JellyTitan/ErgoDonk-Zero/docs/images/1N4001_diode_bending-250w.webp

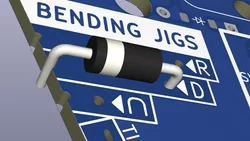
docs/images/1N4001_diode_bending-250w.webp
