JellyTitan/ErgoDonk-Zero/docs/images/3d_model_of_work_feet-250w.webp

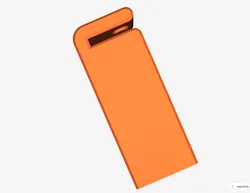
docs/images/3d_model_of_work_feet-250w.webp
