JellyTitan/ErgoDonk-Zero/docs/images/acrylic_case/acrylic_handsome_stack-250w.webp

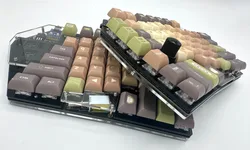
docs/images/acrylic_case/acrylic_handsome_stack-250w.webp
