JellyTitan/ErgoDonk-Zero/docs/images/acrylic_case/acrylic_lh_mcu_cover-400w.webp

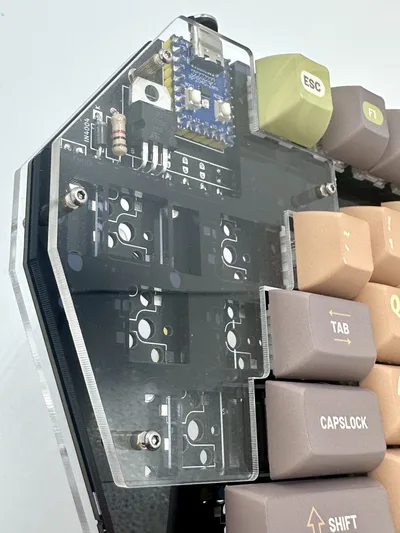
docs/images/acrylic_case/acrylic_lh_mcu_cover-400w.webp
