JellyTitan/ErgoDonk-Zero/docs/images/acrylic_case/acrylic_rh_mcu_cover-250w.webp

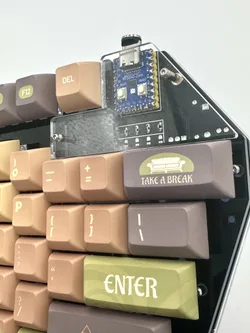
docs/images/acrylic_case/acrylic_rh_mcu_cover-250w.webp
