JellyTitan/ErgoDonk-Zero/docs/images/acrylic_case/acrylic_tilted_hero-250w.webp

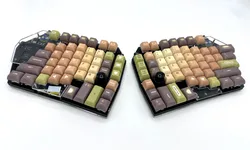
docs/images/acrylic_case/acrylic_tilted_hero-250w.webp
