JellyTitan/ErgoDonk-Zero/docs/images/acrylic_case/backplate-250w.webp

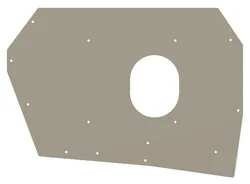
docs/images/acrylic_case/backplate-250w.webp
