JellyTitan/ErgoDonk-Zero/docs/images/acrylic_case/bumper_locations-250w.webp

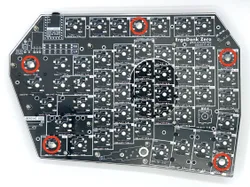
docs/images/acrylic_case/bumper_locations-250w.webp
