JellyTitan/ErgoDonk-Zero/docs/images/acrylic_case/keyplate-250w.webp

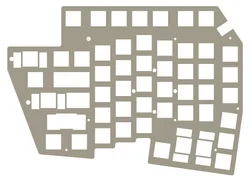
docs/images/acrylic_case/keyplate-250w.webp
