JellyTitan/ErgoDonk-Zero/docs/images/acrylic_case/knob_close_up-800w.webp

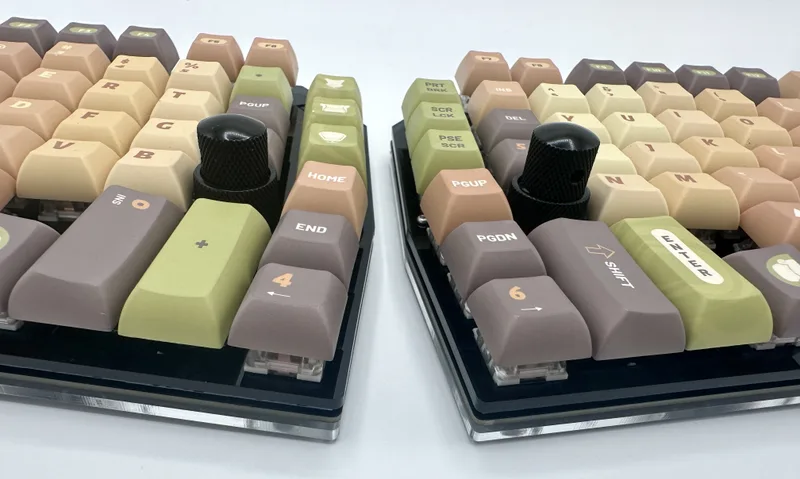
docs/images/acrylic_case/knob_close_up-800w.webp
