JellyTitan/ErgoDonk-Zero/docs/images/acrylic_case/LH_MCU_cover-150w.webp

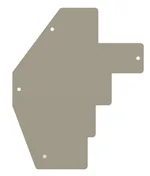
docs/images/acrylic_case/LH_MCU_cover-150w.webp
