JellyTitan/ErgoDonk-Zero/docs/images/acrylic_case/m2_9mm_standoff-250w.webp

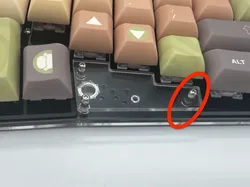
docs/images/acrylic_case/m2_9mm_standoff-250w.webp
