JellyTitan/ErgoDonk-Zero/docs/images/acrylic_case/m2_9mm_standoff.png

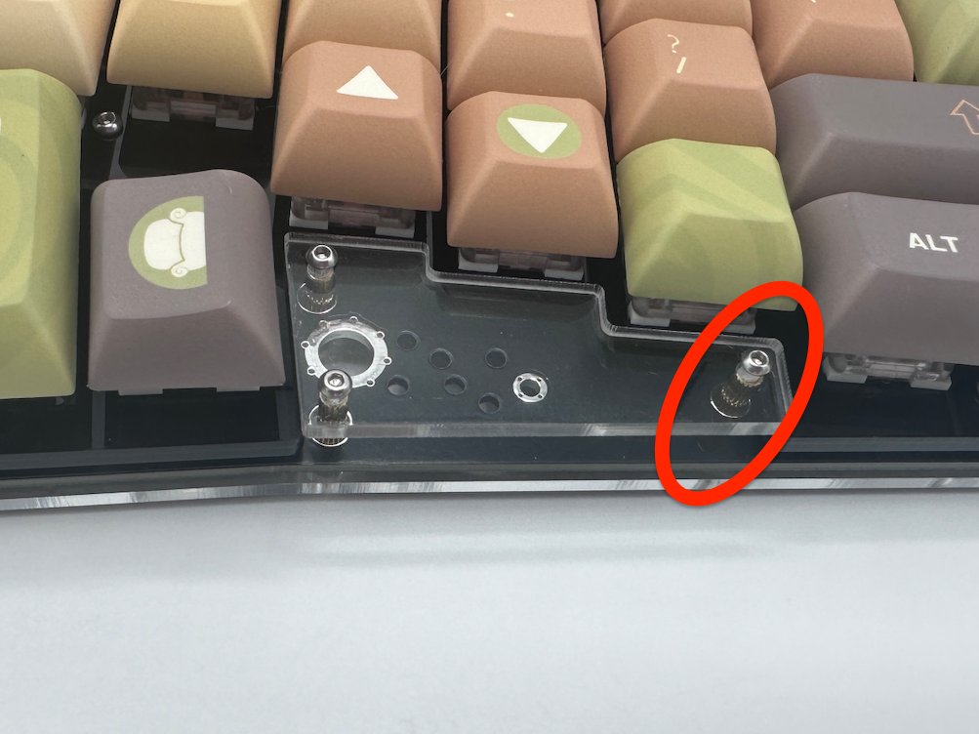
docs/images/acrylic_case/m2_9mm_standoff.png
