JellyTitan/ErgoDonk-Zero/docs/images/acrylic_case/m2_16mm_standoff.png

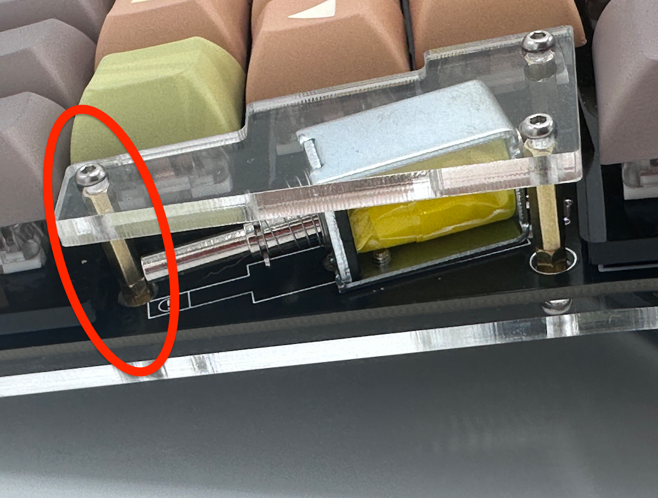
docs/images/acrylic_case/m2_16mm_standoff.png
