JellyTitan/ErgoDonk-Zero/docs/images/acrylic_case/RH_MCU_cover-400w.webp

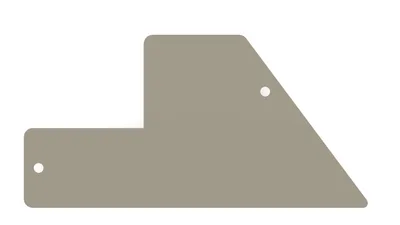
docs/images/acrylic_case/RH_MCU_cover-400w.webp
