JellyTitan/ErgoDonk-Zero/docs/images/acrylic_case/solenoid_blank_cover_plate_RH-1200w.webp

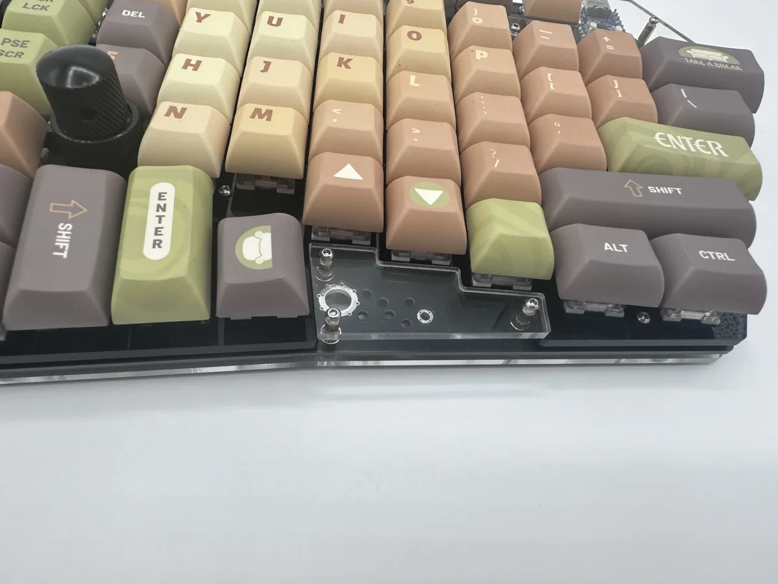
docs/images/acrylic_case/solenoid_blank_cover_plate_RH-1200w.webp
