JellyTitan/ErgoDonk-Zero/docs/images/acrylic_case/solenoid_cover-250w.webp

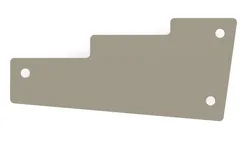
docs/images/acrylic_case/solenoid_cover-250w.webp
