JellyTitan/ErgoDonk-Zero/docs/images/acrylic_case/solenoid_cover_plate_LH-1600w.webp

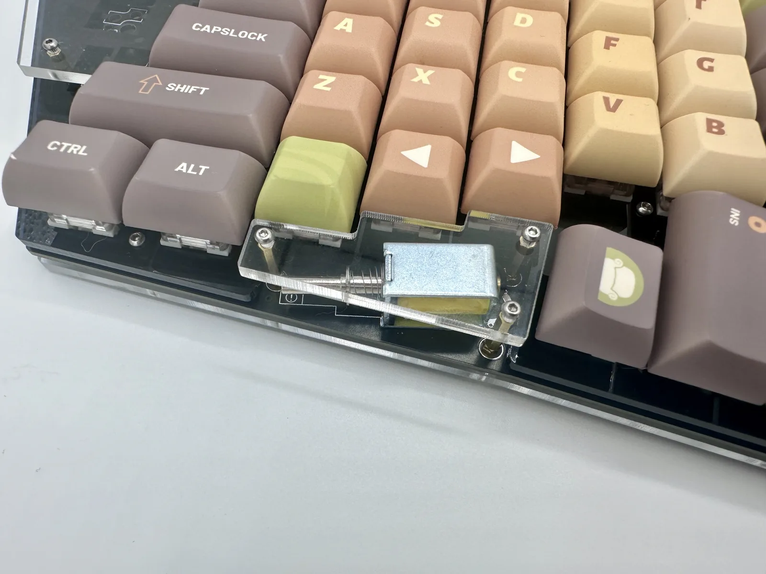
docs/images/acrylic_case/solenoid_cover_plate_LH-1600w.webp
