JellyTitan/ErgoDonk-Zero/docs/images/asymmetrical_diode_marking-250w.webp

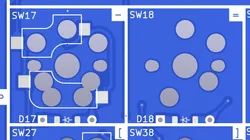
docs/images/asymmetrical_diode_marking-250w.webp
