JellyTitan/ErgoDonk-Zero/docs/images/asymmetrical_diode_marking.webp

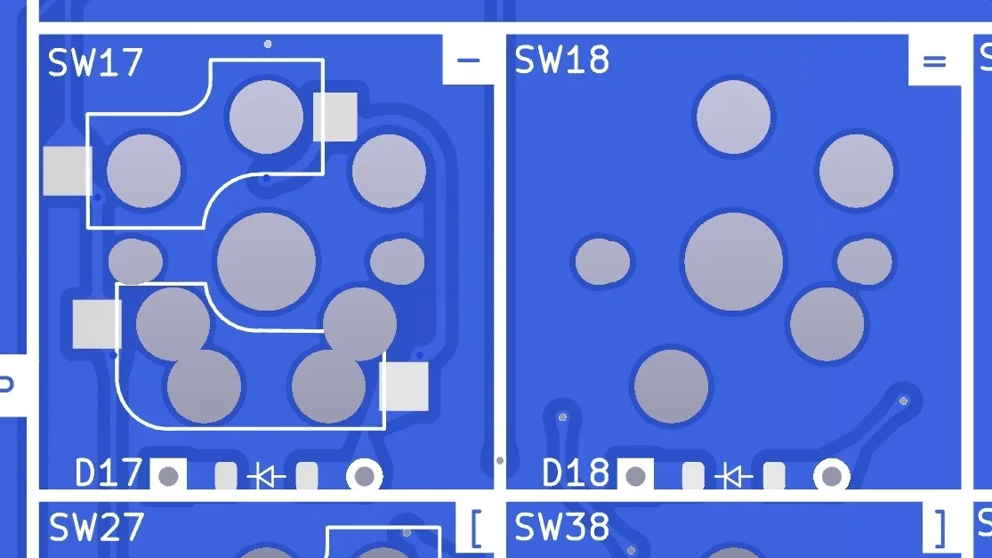
docs/images/asymmetrical_diode_marking.webp
