JellyTitan/ErgoDonk-Zero/docs/images/carpenter_pencil-250w.webp

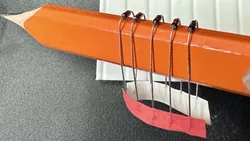
docs/images/carpenter_pencil-250w.webp
