JellyTitan/ErgoDonk-Zero/docs/images/clipping_jumpers-150w.webp

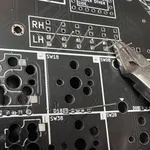
docs/images/clipping_jumpers-150w.webp
