JellyTitan/ErgoDonk-Zero/docs/images/diode_bend_top-1200w.webp

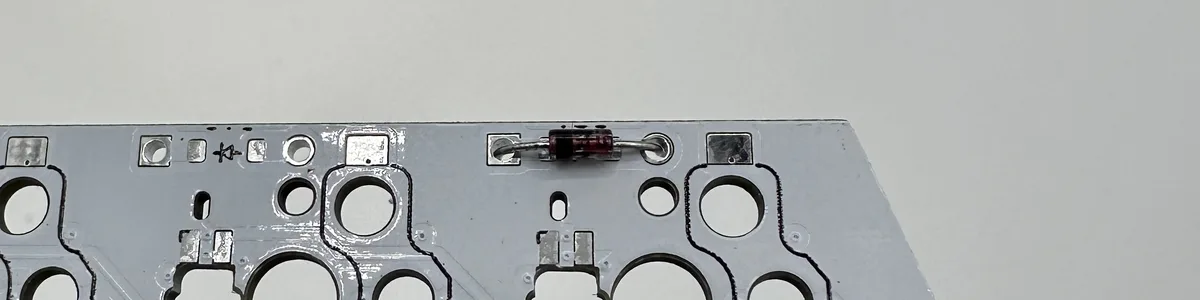
docs/images/diode_bend_top-1200w.webp
