JellyTitan/ErgoDonk-Zero/docs/images/diode_bend_under-800w.webp

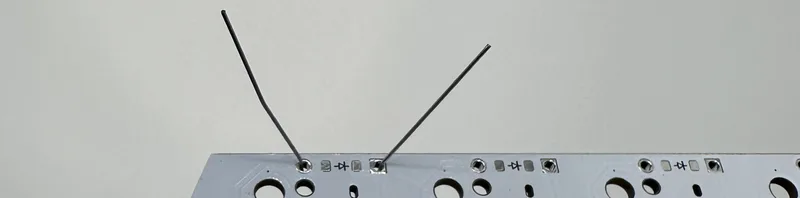
docs/images/diode_bend_under-800w.webp
