JellyTitan/ErgoDonk-Zero/docs/images/diode_jig_cut-400w.webp

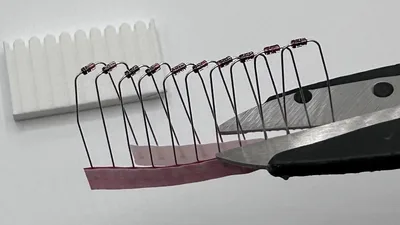
docs/images/diode_jig_cut-400w.webp
