JellyTitan/ErgoDonk-Zero/docs/images/diode_jig_fold-250w.webp

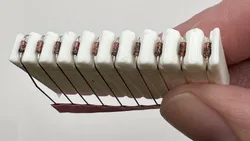
docs/images/diode_jig_fold-250w.webp
