JellyTitan/ErgoDonk-Zero/docs/images/diodes-150w.webp

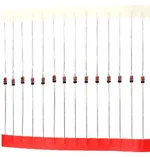
docs/images/diodes-150w.webp
