JellyTitan/ErgoDonk-Zero/docs/images/ec11-150w.webp

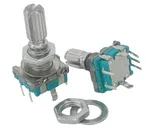
docs/images/ec11-150w.webp
