JellyTitan/ErgoDonk-Zero/docs/images/ec11_knob-450w.webp

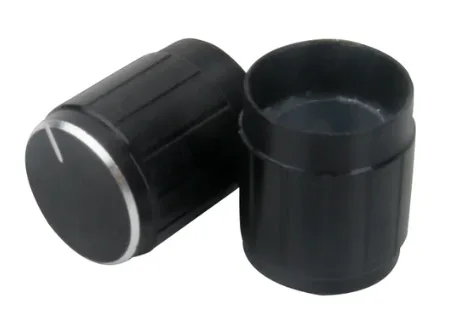
docs/images/ec11_knob-450w.webp
