JellyTitan/ErgoDonk-Zero/docs/images/ergodonk_bristling_with_diodes-800w.webp

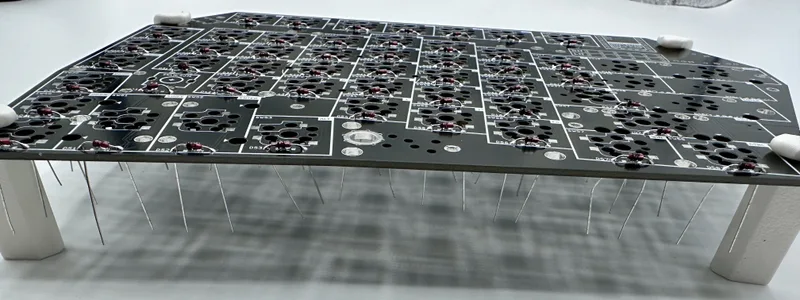
docs/images/ergodonk_bristling_with_diodes-800w.webp
