JellyTitan/ErgoDonk-Zero/docs/images/ergodonk_lh_sockets-1600w.webp

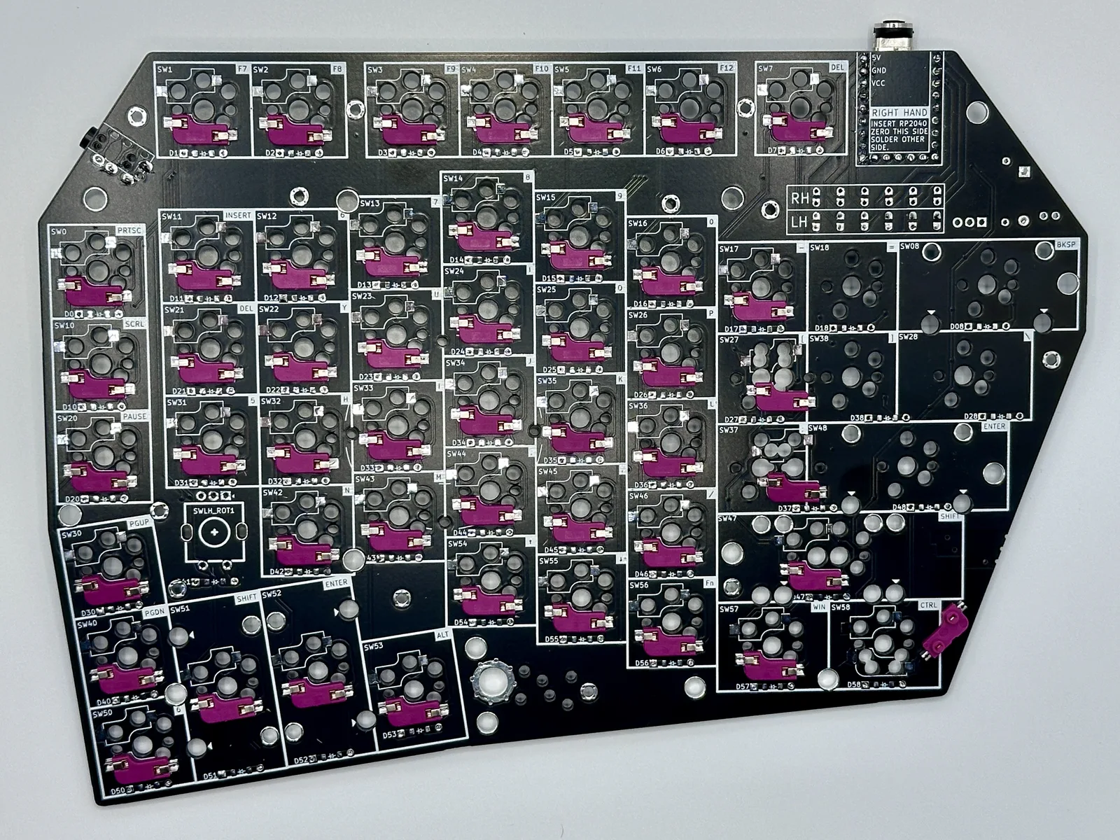
docs/images/ergodonk_lh_sockets-1600w.webp
