JellyTitan/ErgoDonk-Zero/docs/images/ergodonk_monobody_case-250w.webp

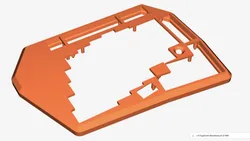
docs/images/ergodonk_monobody_case-250w.webp
