JellyTitan/ErgoDonk-Zero/docs/images/ergodonk_rh_sockets-250w.webp

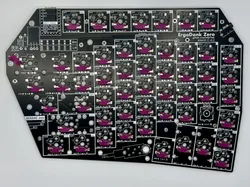
docs/images/ergodonk_rh_sockets-250w.webp
