JellyTitan/ErgoDonk-Zero/docs/images/ErgoDonk_row_heights-400w.webp

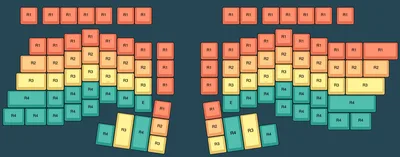
docs/images/ErgoDonk_row_heights-400w.webp
