JellyTitan/ErgoDonk-Zero/docs/images/ErgoDonk_zero_all_feet-400w.webp

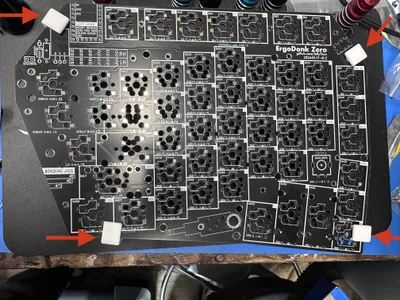
docs/images/ErgoDonk_zero_all_feet-400w.webp
