JellyTitan/ErgoDonk-Zero/docs/images/ergodonk_zero_keyplate-400w.webp

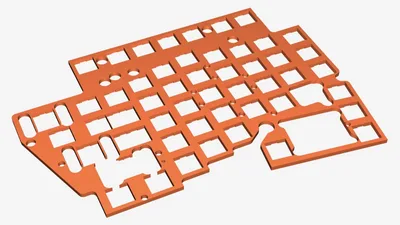
docs/images/ergodonk_zero_keyplate-400w.webp
