JellyTitan/ErgoDonk-Zero/docs/images/Ergodonk_zero_one_foot-4032w.webp

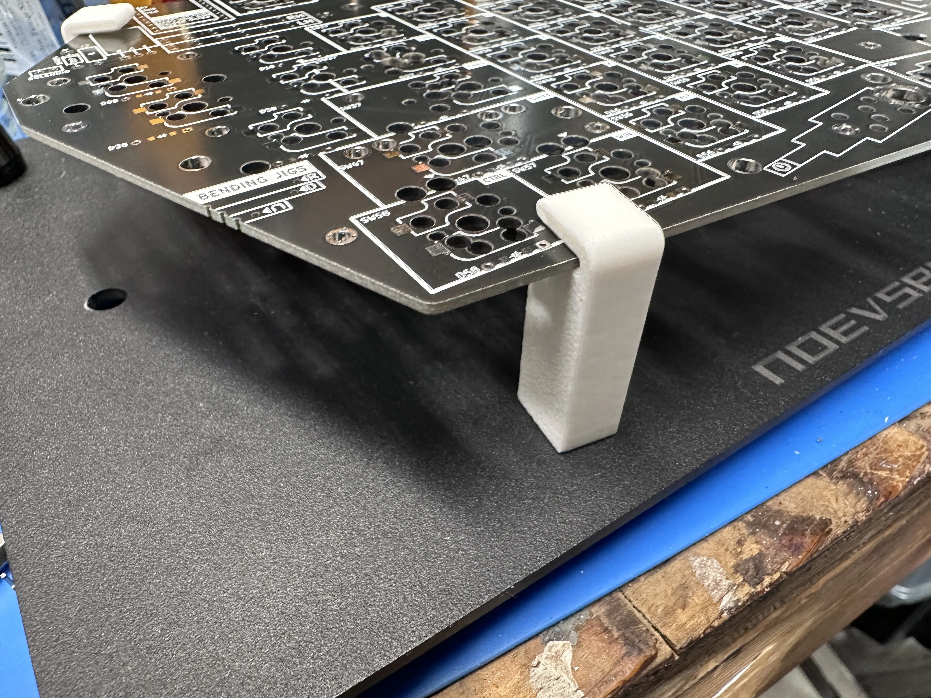
docs/images/Ergodonk_zero_one_foot-4032w.webp
