JellyTitan/ErgoDonk-Zero/docs/images/fdm_case/fdm_donk_2-400w.webp

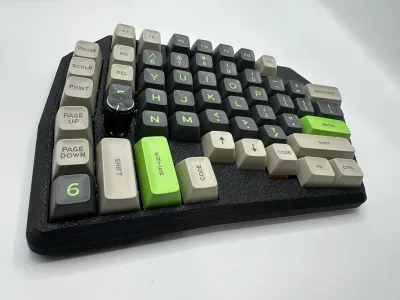
docs/images/fdm_case/fdm_donk_2-400w.webp
