JellyTitan/ErgoDonk-Zero/docs/images/fdm_case/fdm_donk_3-250w.webp

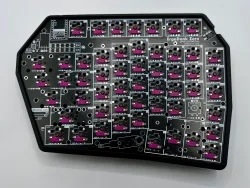
docs/images/fdm_case/fdm_donk_3-250w.webp
