JellyTitan/ErgoDonk-Zero/docs/images/fdm_case/fdm_donk_cases_hero.jpeg

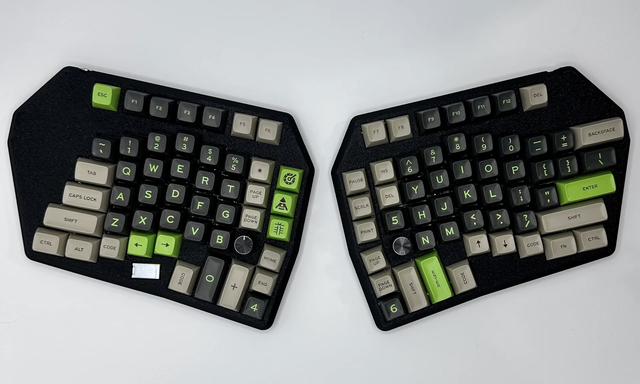
docs/images/fdm_case/fdm_donk_cases_hero.jpeg
