JellyTitan/ErgoDonk-Zero/docs/images/hot_swop_sockets-250w.webp

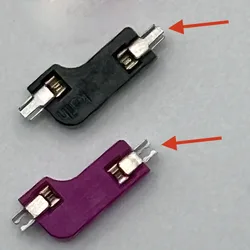
docs/images/hot_swop_sockets-250w.webp
