JellyTitan/ErgoDonk-Zero/docs/images/jumper_bender_use-150w.webp

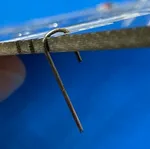
docs/images/jumper_bender_use-150w.webp
