JellyTitan/ErgoDonk-Zero/docs/images/jumpers-208w.webp

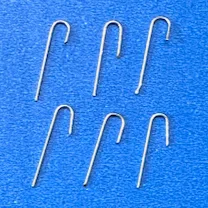
docs/images/jumpers-208w.webp
