JellyTitan/ErgoDonk-Zero/docs/images/jumpers_in_place-400w.webp

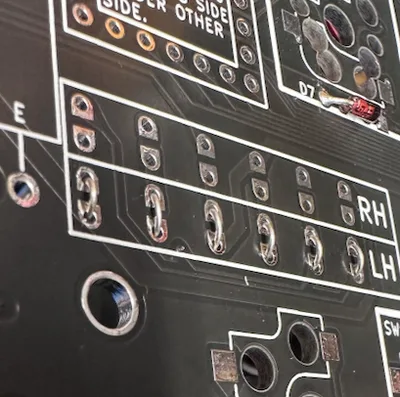
docs/images/jumpers_in_place-400w.webp
