JellyTitan/ErgoDonk-Zero/docs/images/kapton_under-1600w.webp

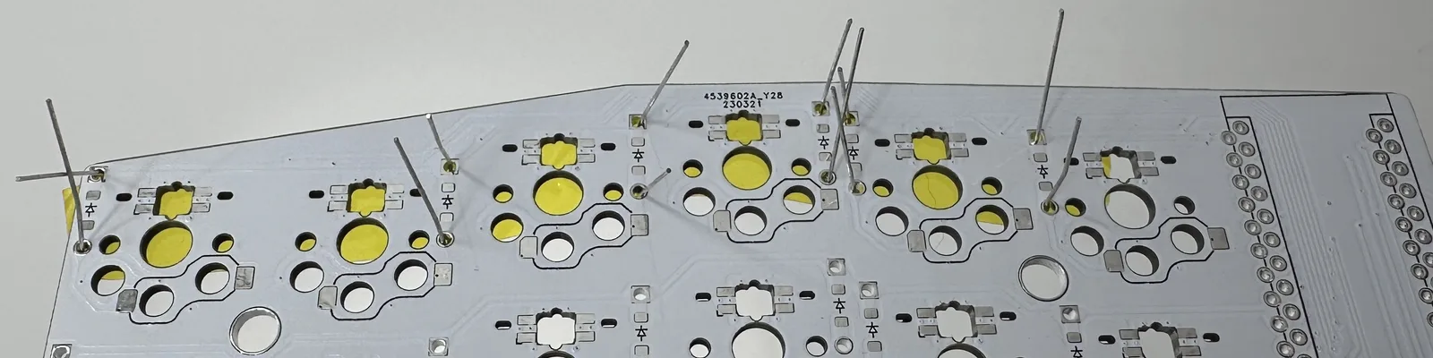
docs/images/kapton_under-1600w.webp
