JellyTitan/ErgoDonk-Zero/docs/images/LH_backside_diode-1600w.webp

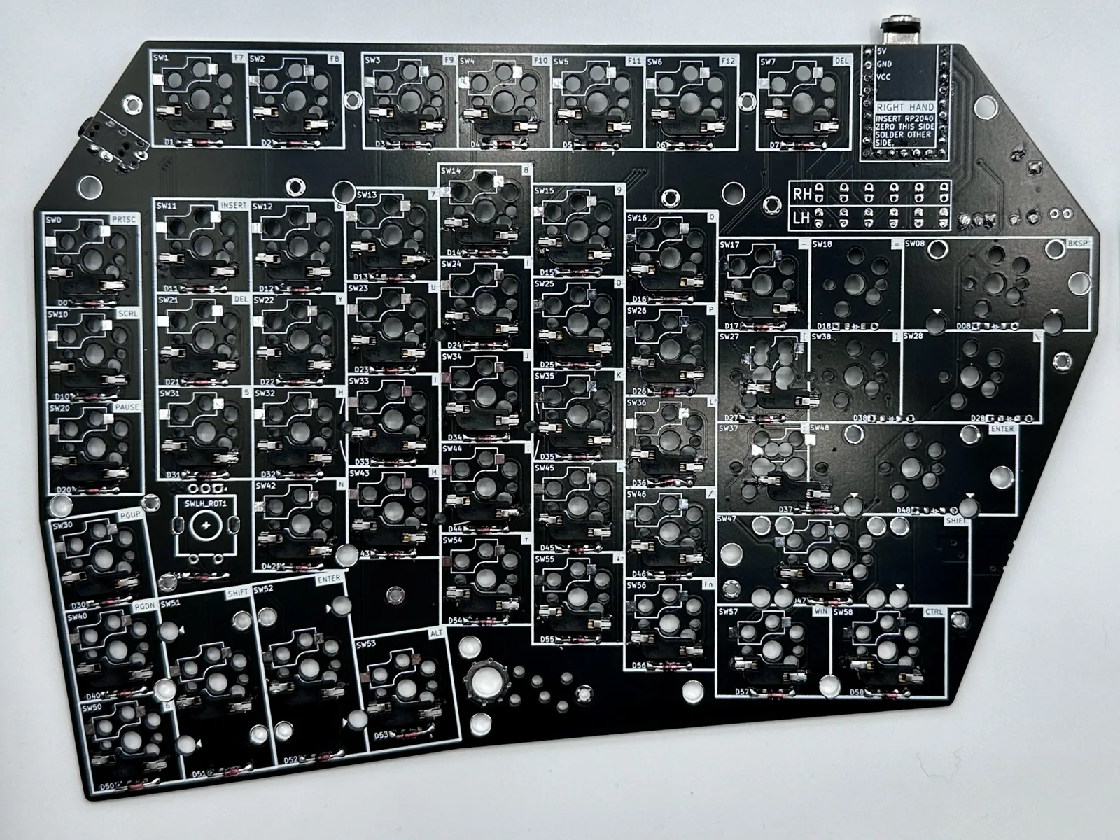
docs/images/LH_backside_diode-1600w.webp
