JellyTitan/ErgoDonk-Zero/docs/images/line_up_the_zero-250w.webp

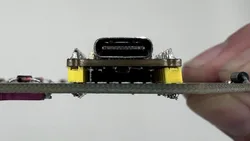
docs/images/line_up_the_zero-250w.webp
