JellyTitan/ErgoDonk-Zero/docs/images/mcu_top_of_board_1-250w.webp

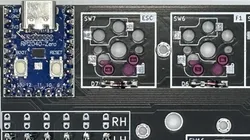
docs/images/mcu_top_of_board_1-250w.webp
