JellyTitan/ErgoDonk-Zero/docs/images/mcu_top_of_board_2-1200w.webp

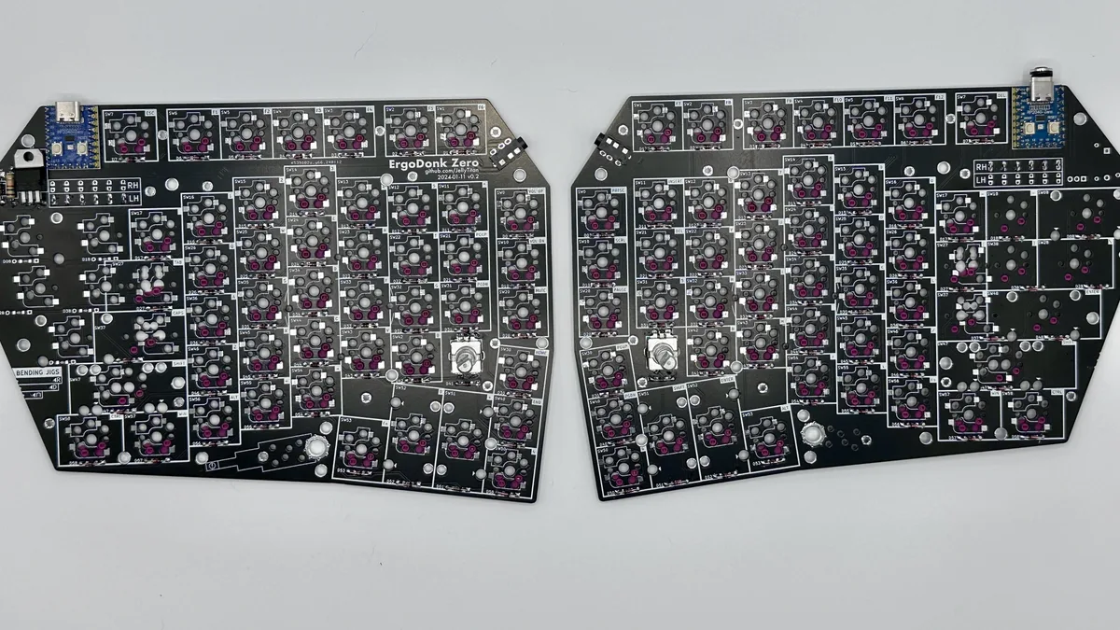
docs/images/mcu_top_of_board_2-1200w.webp
