JellyTitan/ErgoDonk-Zero/docs/images/mvp_case/mvp_case_back-250w.webp

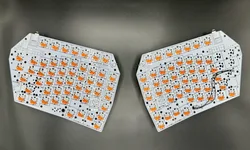
docs/images/mvp_case/mvp_case_back-250w.webp
