JellyTitan/ErgoDonk-Zero/docs/images/mvp_case/mvp_case_both-800w.webp

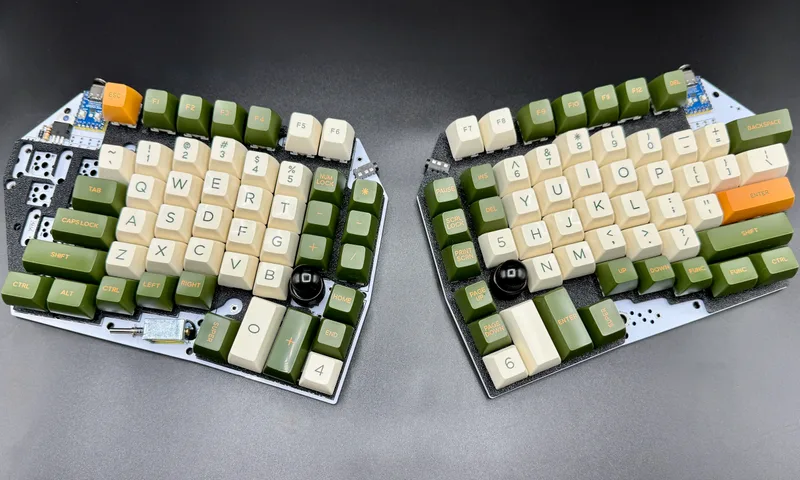
docs/images/mvp_case/mvp_case_both-800w.webp
