JellyTitan/ErgoDonk-Zero/docs/images/mvp_case/mvp_case_left_closeup-250w.webp

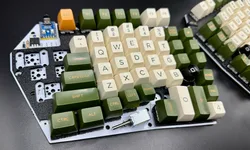
docs/images/mvp_case/mvp_case_left_closeup-250w.webp
