JellyTitan/ErgoDonk-Zero/docs/images/pad_nub-175w.webp

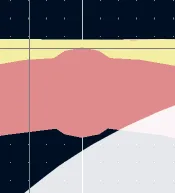
docs/images/pad_nub-175w.webp
