JellyTitan/ErgoDonk-Zero/docs/images/qmk/ergodonk_zero_qmk_default_keymap.png

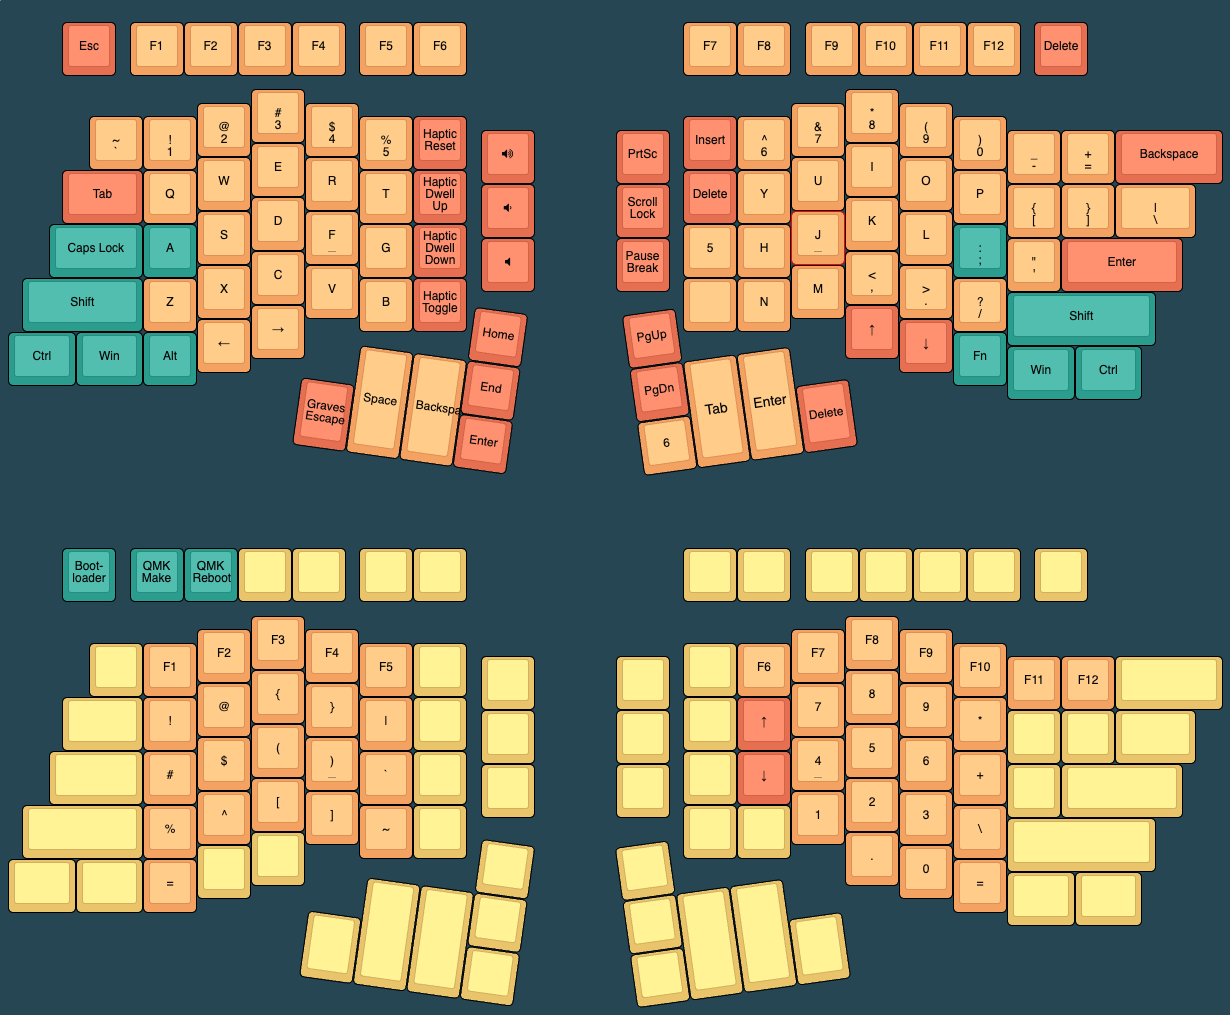
docs/images/qmk/ergodonk_zero_qmk_default_keymap.png
