JellyTitan/ErgoDonk-Zero/docs/images/resistor_bending-400w.webp

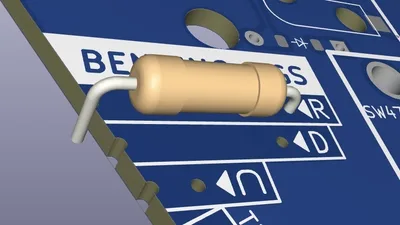
docs/images/resistor_bending-400w.webp
