JellyTitan/ErgoDonk-Zero/docs/images/RH_backside_diode-1200w.webp

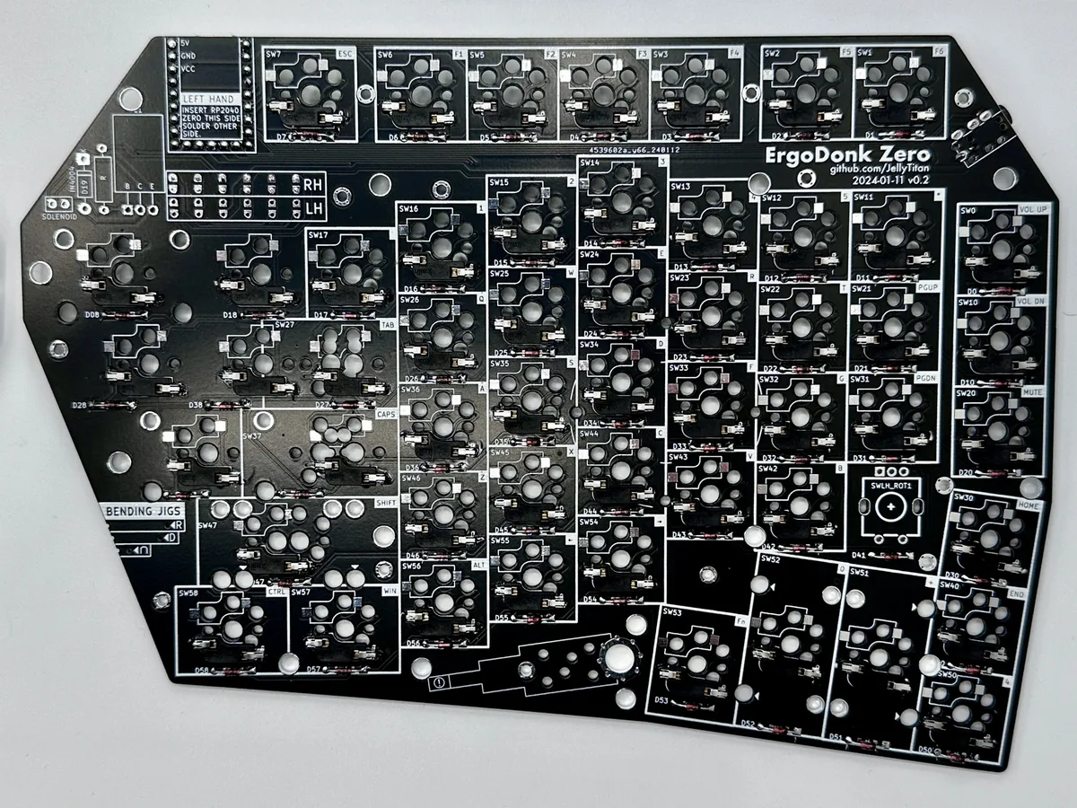
docs/images/RH_backside_diode-1200w.webp
