JellyTitan/ErgoDonk-Zero/docs/images/rp2040-250w.webp

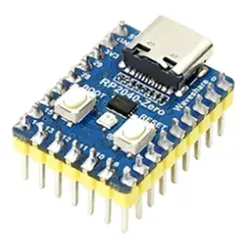
docs/images/rp2040-250w.webp
