JellyTitan/ErgoDonk-Zero/docs/images/sa_heights-400w.webp

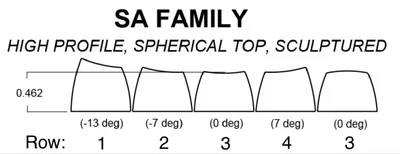
docs/images/sa_heights-400w.webp
