JellyTitan/ErgoDonk-Zero/docs/images/solenoid_circuit-1200w.webp

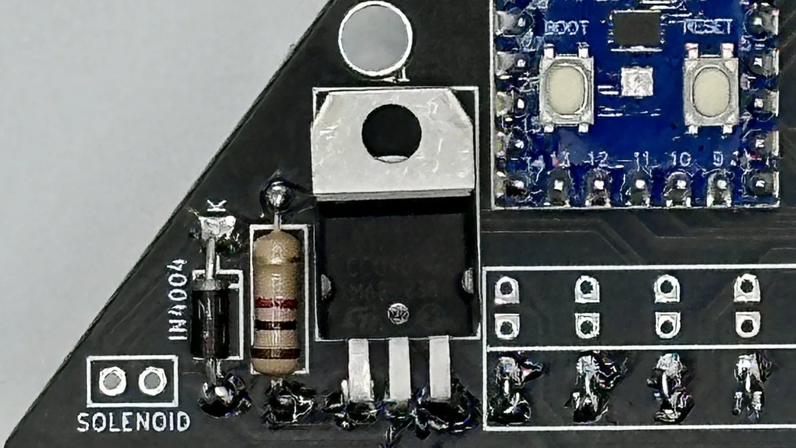
docs/images/solenoid_circuit-1200w.webp
