JellyTitan/ErgoDonk-Zero/docs/images/solenoid_circuit_tip120-250w.webp

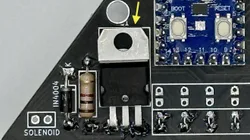
docs/images/solenoid_circuit_tip120-250w.webp
