JellyTitan/ErgoDonk-Zero/docs/images/Solenoid_on_front-1600w.webp

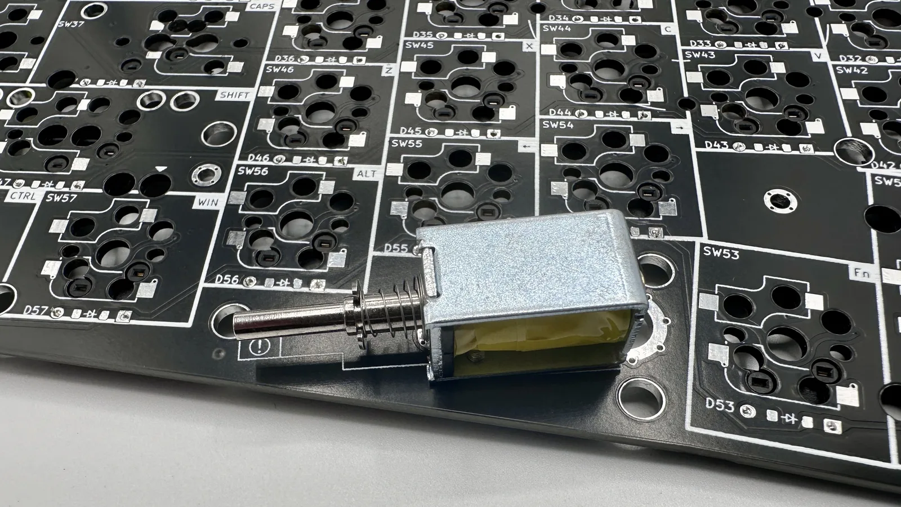
docs/images/Solenoid_on_front-1600w.webp
