JellyTitan/ErgoDonk-Zero/docs/images/solenoid_pin_nipping-400w.webp

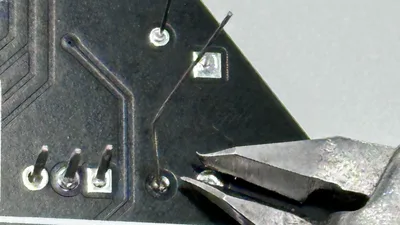
docs/images/solenoid_pin_nipping-400w.webp
