JellyTitan/ErgoDonk-Zero/docs/images/solenoids-250w.webp

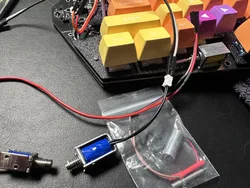
docs/images/solenoids-250w.webp
