JellyTitan/ErgoDonk-Zero/docs/images/stab_prob-250w.webp

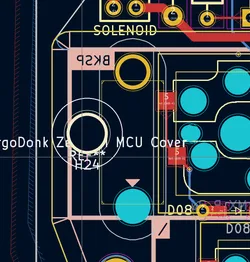
docs/images/stab_prob-250w.webp
