JellyTitan/ErgoDonk-Zero/docs/images/stabilizer_markings-811w.webp

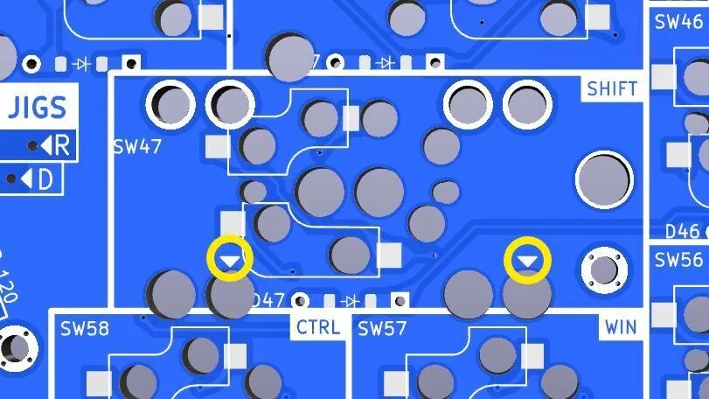
docs/images/stabilizer_markings-811w.webp
