JellyTitan/ErgoDonk-Zero/docs/images/thumb_stabs-250w.webp

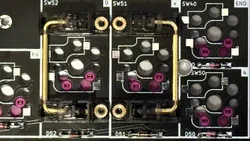
docs/images/thumb_stabs-250w.webp
