JellyTitan/ErgoDonk-Zero/docs/images/tip_120_jig_front-250w.webp

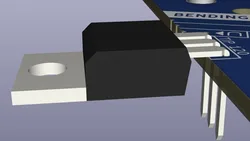
docs/images/tip_120_jig_front-250w.webp
