JellyTitan/ErgoDonk-Zero/docs/images/tip_tape_trim_3-150w.webp

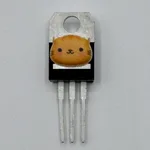
docs/images/tip_tape_trim_3-150w.webp
