JellyTitan/ErgoDonk-Zero/docs/images/top_jig-1600w.webp

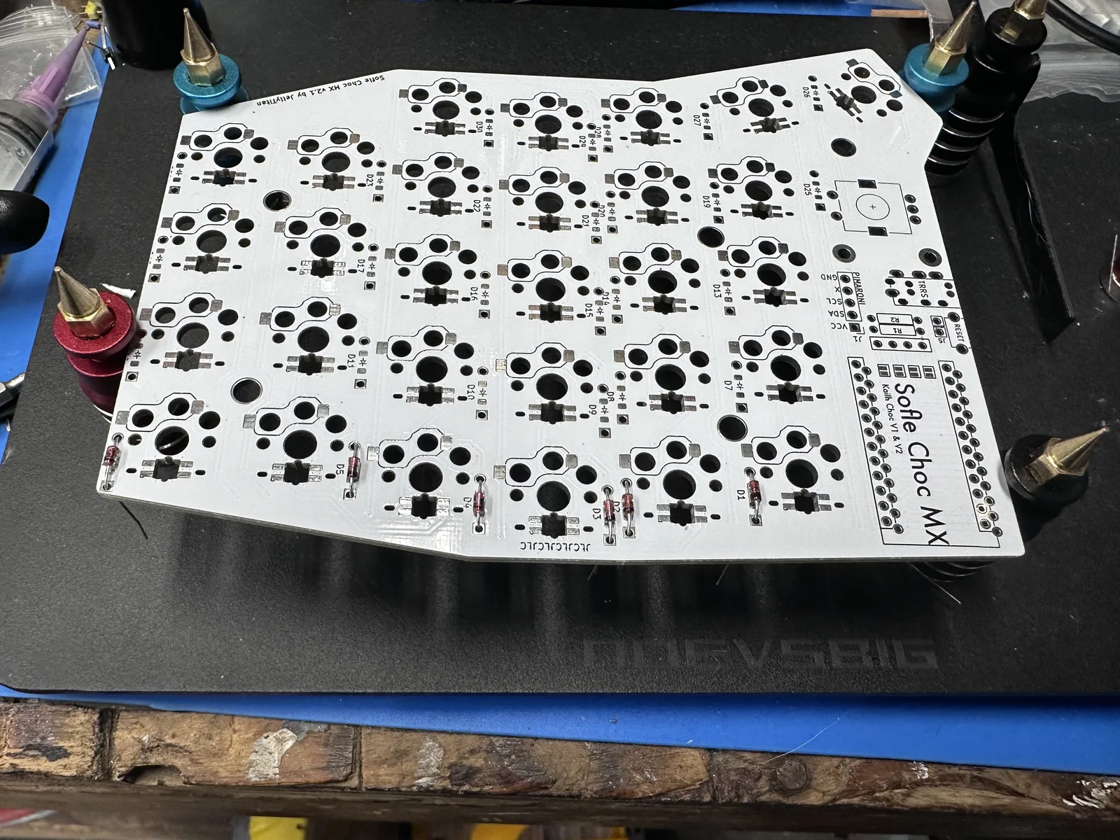
docs/images/top_jig-1600w.webp
