JellyTitan/ErgoDonk-Zero/docs/images/TRRS_back-400w.webp

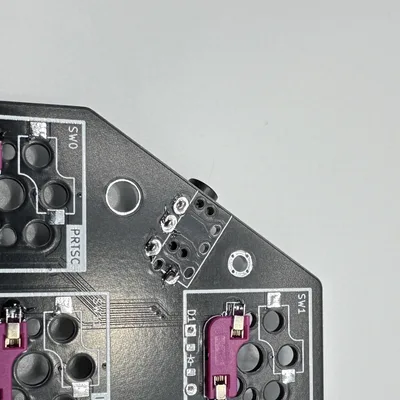
docs/images/TRRS_back-400w.webp
