JellyTitan/ErgoDonk-Zero/docs/images/TRRS_front-250w.webp

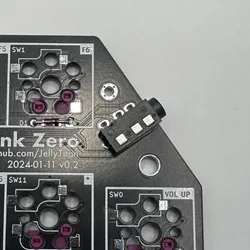
docs/images/TRRS_front-250w.webp
