JellyTitan/ErgoDonk-Zero/docs/images/trs_cable-150w.webp

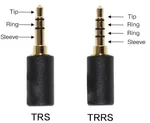
docs/images/trs_cable-150w.webp
