JellyTitan/ErgoDonk-Zero/docs/images/VIA/via_1-250w.webp

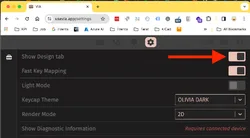
docs/images/VIA/via_1-250w.webp
