JellyTitan/ErgoDonk-Zero/docs/images/VIA/via_2-400w.webp

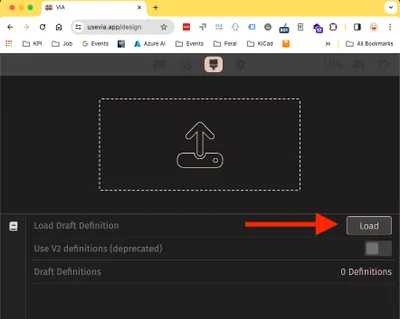
docs/images/VIA/via_2-400w.webp
