JellyTitan/ErgoDonk-Zero/docs/images/VIA/via_3-250w.webp

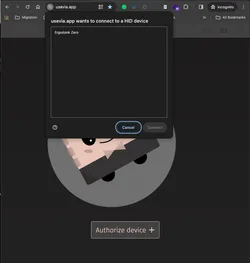
docs/images/VIA/via_3-250w.webp
