JellyTitan/ErgoDonk-Zero/docs/images/VIA/via_3-800w.webp

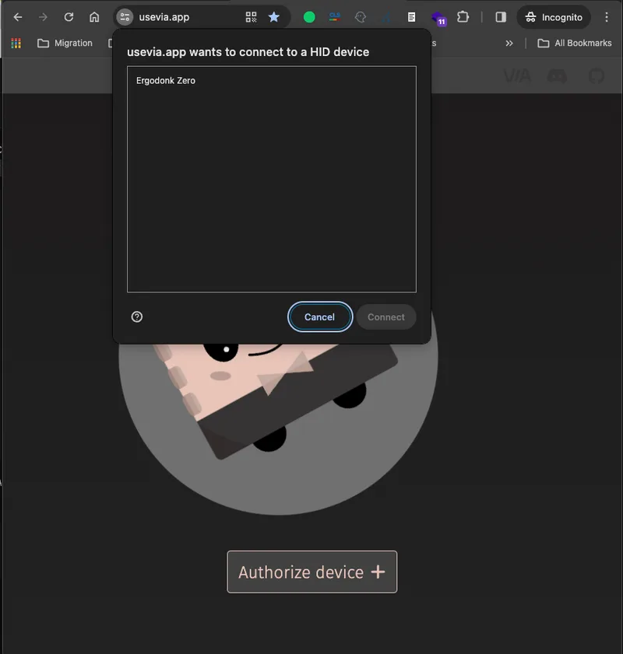
docs/images/VIA/via_3-800w.webp
