JellyTitan/ErgoDonk-Zero/docs/web-app-manifest-512x512.png

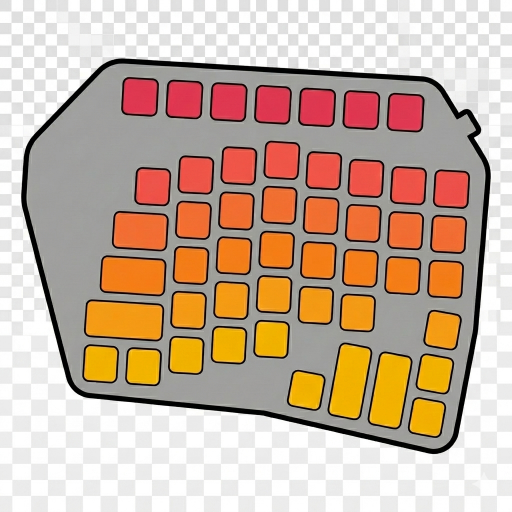
docs/web-app-manifest-512x512.png
