JellyTitan/ErgoDonk-Zero/docs/images/ordering_guide/JLCPCB_Ordering_2-150w.webp

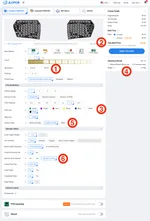
docs/images/ordering_guide/JLCPCB_Ordering_2-150w.webp
