JellyTitan/ErgoDonk-Zero/docs/images/mvp_case/mvp_case_print_settings-150w.webp

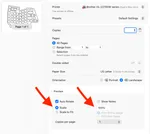
docs/images/mvp_case/mvp_case_print_settings-150w.webp
