JellyTitan/ErgoDonk-Zero/docs/images/mvp_case/mvp_case_print_settings-250w.webp

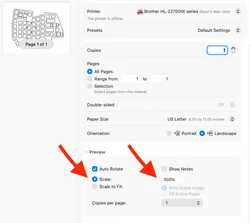
docs/images/mvp_case/mvp_case_print_settings-250w.webp
