JellyTitan/ErgoDonk-Zero/docs/images/build-log/riverbottom_ergodonk_nameshare-150w.webp

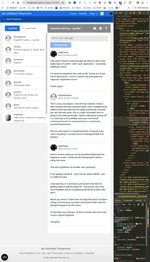
docs/images/build-log/riverbottom_ergodonk_nameshare-150w.webp
