JellyTitan/ErgoDonk-Zero/PCB/ergodonk_simple_zero.kicad_sch

## KiCad design PCB/ergodonk_simple_zero.kicad_sch (2024-07-03)

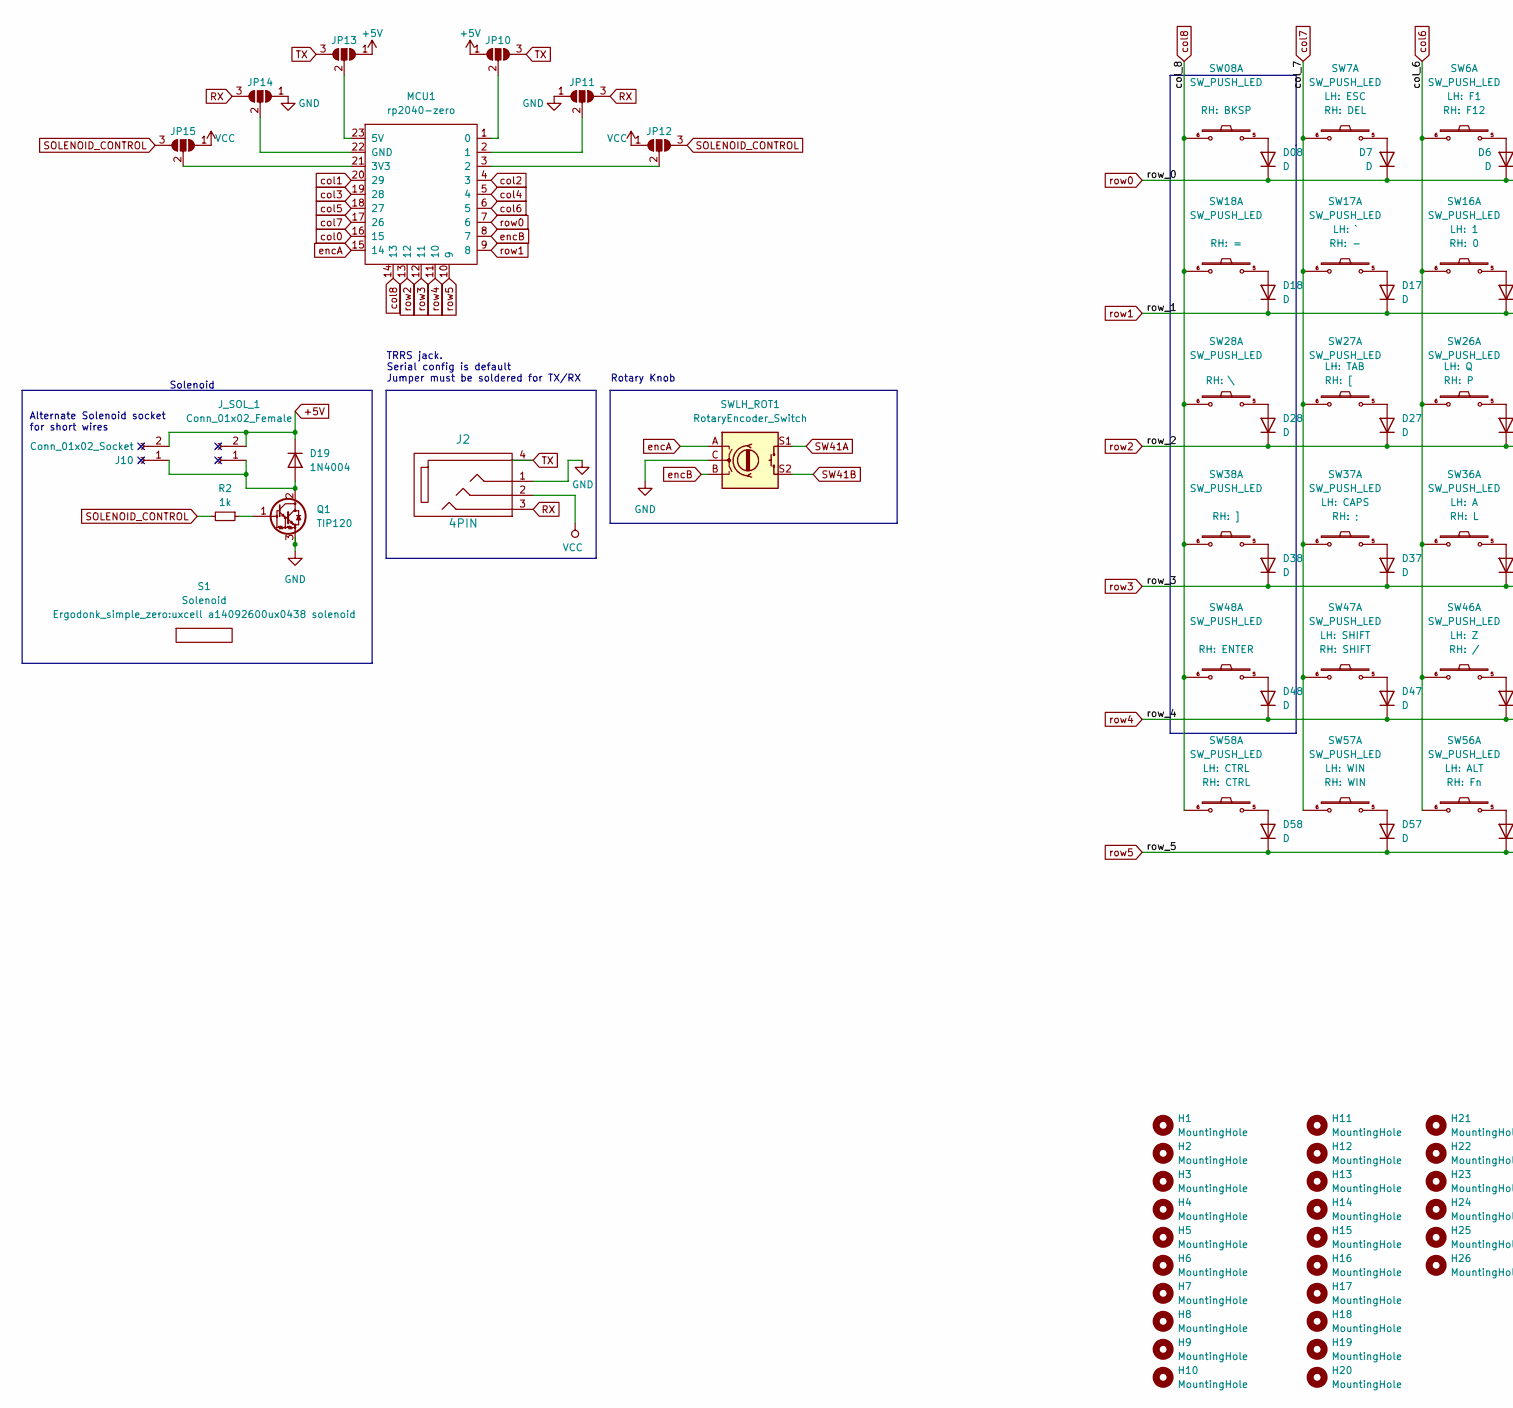
[picture p171: schematic ergodonk_simple_zero.kicad_sch, part in row 1, column 1]

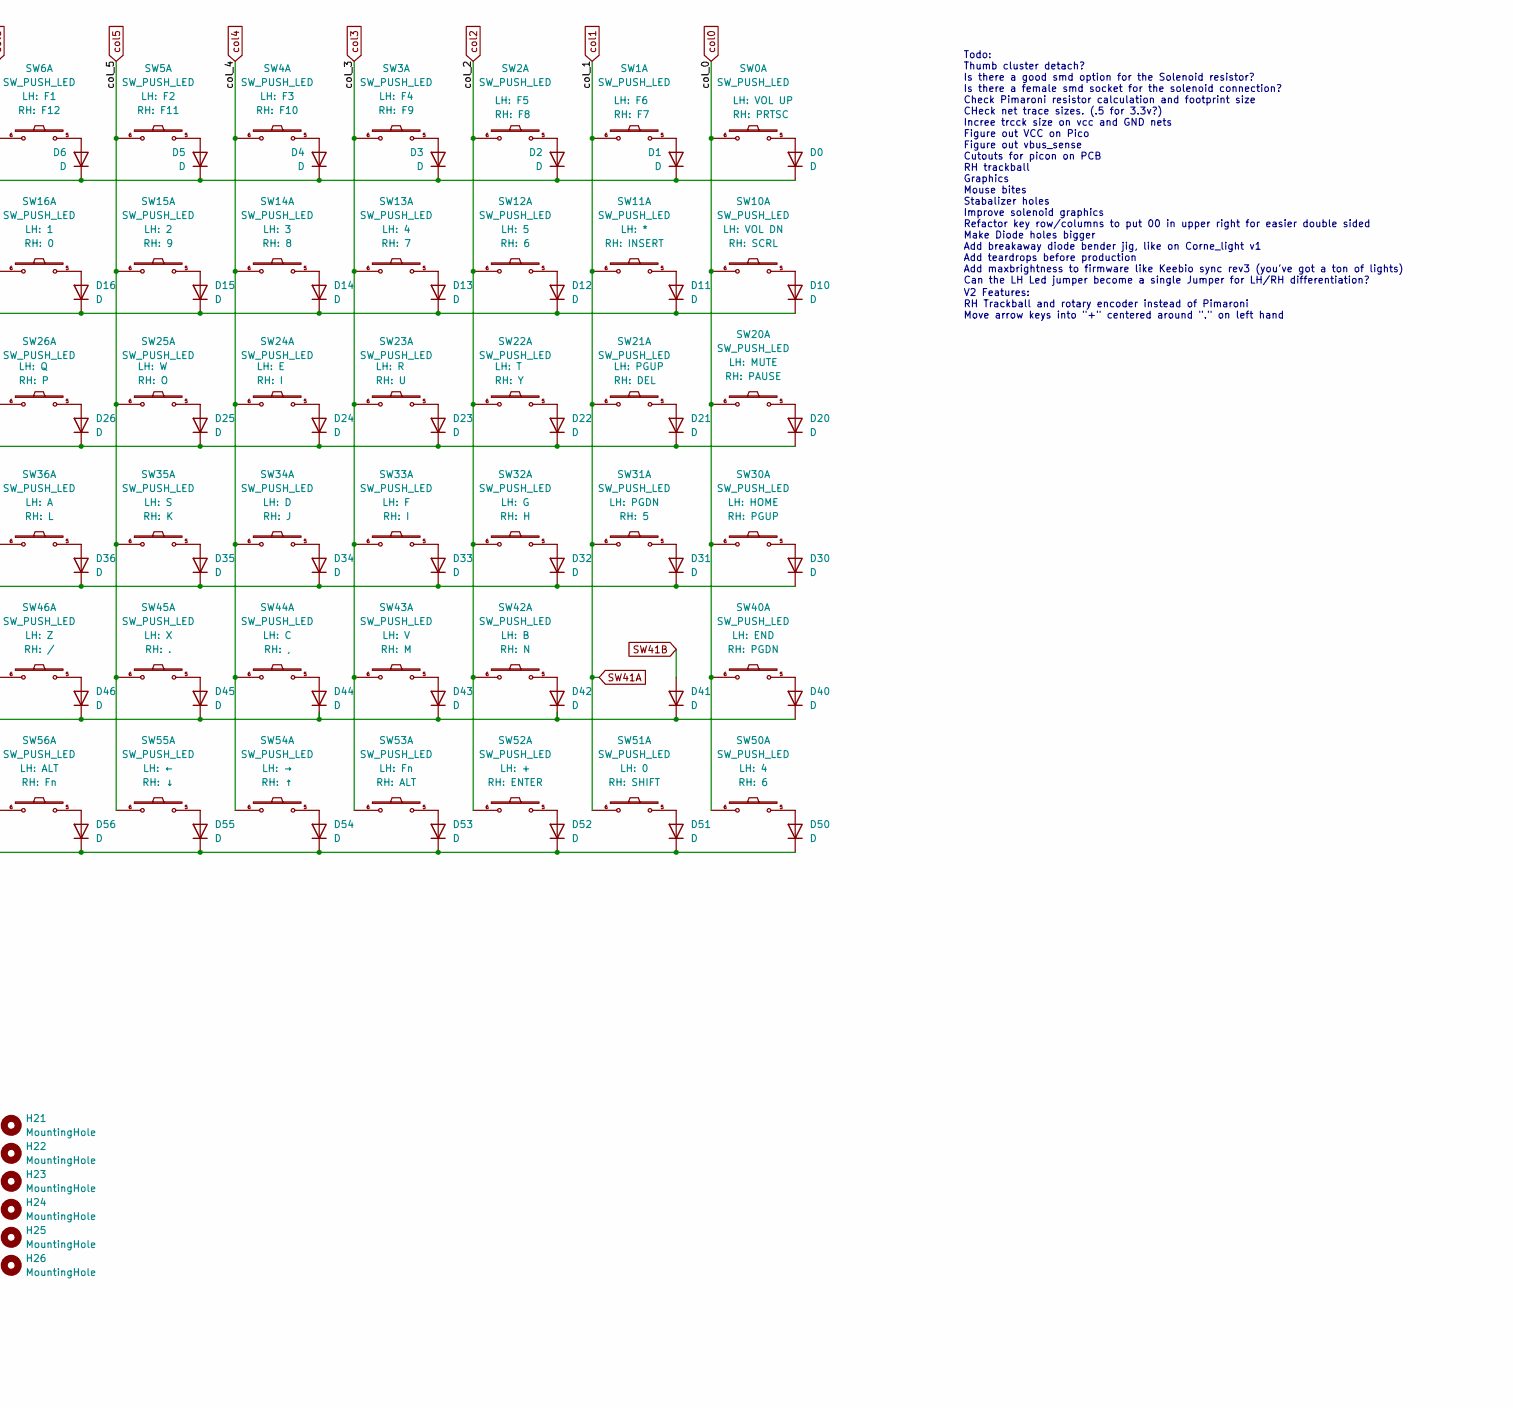
[picture p172: schematic ergodonk_simple_zero.kicad_sch, part in row 1, column 2]

Parts:
D0, D1, D2, D3, D4, D5, D6, D7, D08, D10, D11, D12, D13, D14, D15, D16, D17, D18, D20, D21, D22, D23, D24, D25, D26, D27, D28, D30, D31, D32, D33, D34, D35, D36, D37, D38, D40, D41, D42, D43, D44, D45, D46, D47, D48, D50, D51, D52, D53, D54, D55, D56, D57, D58: D; D_SOD-123_DO-35_Hybrid_DoubleSided_ergodonk_simple_zero
D19: 1N4004; D_DO-41_SOD81_P10.16mm_Horizontal
H1, H2, H3, H5, H6, H7, H8, H9, H10, H26: MountingHole; Hole from sofle for M2 posts gold rimmer
H4, H20, H24: MountingHole; M2 Standoff hole - keyplate passthrough
H11, H12, H13, H14, H15, H16, H17, H18, H19, H21, H22, H23, H25: MountingHole; M2_Hole_fancy_for_bolt-on-plate
J2: 4PIN; MJ-4PP-9_TRRS_ds_jack
J10: Conn_01x02_Socket; PinHeader_1x02_P2.54mm_Vertical
JP10, JP11, JP12, JP13, JP14, JP15: SolderJumper_3_Open; Level Shifter Bypass Jumper simple_zero
J_SOL_1: Conn_01x02_Female; PinHeader_1x02_P2.54mm_Vertical
MCU1: rp2040-zero; rp2040 Zero simple_zero
Q1: TIP120; TO-220-3_Horizontal_TabDown_ergodonk_simple_zero
R2: 1k; R_Axial_DIN0309_L9.0mm_D3.2mm_P12.70mm_Horizontal
S1: Solenoid; uxcell a14092600ux0438 solenoid
SW0, SW1, SW2, SW3, SW4, SW5, SW6, SW7, SW10, SW11, SW12, SW13, SW14, SW15, SW16, SW17, SW20, SW21, SW22, SW23, SW24, SW25, SW26, SW30, SW31, SW32, SW33, SW34, SW35, SW36, SW42, SW43, SW44, SW45, SW46, SW50, SW54, SW55, SW56: SW_PUSH_LED; CherryMX_Choc_Hotswap_ergodonk_simple_zero_DS
SW08: SW_PUSH_LED; CherryMX_Choc_Hotswap_ergodonk_simple_zero_SS_2U
SW18, SW38: SW_PUSH_LED; CherryMX_Choc_Hotswap_ergodonk_simple_zero_SS
SW27: SW_PUSH_LED; CherryMX_Choc_Hotswap_ergodonk_simple_zero_SS_1.5uLH_1uRH
SW28: SW_PUSH_LED; CherryMX_Choc_Hotswap_ergodonk_simple_zero_SS_1.5U
SW37: SW_PUSH_LED; CherryMX_Choc_Hotswap_ergodonk_simple_zero_SS_1.75uLH_1uRH
SW40: SW_PUSH_LED; CherryMX_Choc_Hotswap_ergodonk_simple_zero_DS_shave_corner
SW47: SW_PUSH_LED; CherryMX_Choc_Hotswap_ergodonk_simple_zero_SS_2.25uLH 2.75u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
SW48: SW_PUSH_LED; CherryMX_Choc_Hotswap_ergodonk_simple_zero_SS_2.25U
SW51, SW52: SW_PUSH_LED; CherryMX_Choc_Hotswap_ergodonk_simple_zero_DS_2u_vert
SW53: SW_PUSH_LED; CherryMX_Choc_Hotswap_ergodonk_simple_zero_DS_1.25u_vert
SW57, SW58: SW_PUSH_LED; CherryMX_Choc_Hotswap_ergodonk_simple_zero_DS_1.25u
SWLH_ROT1: RotaryEncoder_Switch; RotaryEncoder_EC11_ergodonk_variant

Connections:
+5V: D19.1 (K), J10.2, JP10.1 (A), JP13.1 (A), J_SOL_1.2
GND: J2.1, JP11.1 (A), JP14.1 (A), Q1.3 (E), SWLH_ROT1.C
unnamed: D0.2 (A), SW0.5
unnamed: D1.2 (A), SW1.5
unnamed: D2.2 (A), SW2.5
unnamed: D3.2 (A), SW3.5
unnamed: D4.2 (A), SW4.5
unnamed: D5.2 (A), SW5.5
unnamed: D6.2 (A), SW6.5
unnamed: D7.2 (A), SW7.5
unnamed: D08.2 (A), SW08.5
unnamed: D10.2 (A), SW10.5
unnamed: D11.2 (A), SW11.5
unnamed: D12.2 (A), SW12.5
unnamed: D13.2 (A), SW13.5
unnamed: D14.2 (A), SW14.5
unnamed: D15.2 (A), SW15.5
unnamed: D16.2 (A), SW16.5
unnamed: D17.2 (A), SW17.5
unnamed: D18.2 (A), SW18.5
unnamed: D19.2 (A), J10.1, J_SOL_1.1, Q1.2 (C)
unnamed: D20.2 (A), SW20.5
unnamed: D21.2 (A), SW21.5
unnamed: D22.2 (A), SW22.5
unnamed: D23.2 (A), SW23.5
unnamed: D24.2 (A), SW24.5
unnamed: D25.2 (A), SW25.5
unnamed: D26.2 (A), SW26.5
unnamed: D27.2 (A), SW27.5
unnamed: D28.2 (A), SW28.5
unnamed: D30.2 (A), SW30.5
unnamed: D31.2 (A), SW31.5
unnamed: D32.2 (A), SW32.5
unnamed: D33.2 (A), SW33.5
unnamed: D34.2 (A), SW34.5
unnamed: D35.2 (A), SW35.5
unnamed: D36.2 (A), SW36.5
unnamed: D37.2 (A), SW37.5
unnamed: D38.2 (A), SW38.5
unnamed: D40.2 (A), SW40.5
unnamed: D42.2 (A), SW42.5
unnamed: D43.2 (A), SW43.5
unnamed: D44.2 (A), SW44.5
unnamed: D45.2 (A), SW45.5
unnamed: D46.2 (A), SW46.5
unnamed: D47.2 (A), SW47.5
unnamed: D48.2 (A), SW48.5
unnamed: D50.2 (A), SW50.5
unnamed: D51.2 (A), SW51.5
unnamed: D52.2 (A), SW52.5
unnamed: D53.2 (A), SW53.5
unnamed: D54.2 (A), SW54.5
unnamed: D55.2 (A), SW55.5
unnamed: D56.2 (A), SW56.5
unnamed: D57.2 (A), SW57.5
unnamed: D58.2 (A), SW58.5
unnamed: JP10.2 (C), MCU1.1 (0)
unnamed: JP11.2 (C), MCU1.2 (1)
unnamed: JP12.2 (C), MCU1.3 (2)
unnamed: JP13.2 (C), MCU1.23 (5V)
unnamed: JP14.2 (C), MCU1.22 (GND)
unnamed: JP15.2 (C), MCU1.21 (3V3)
unnamed: Q1.1 (B), R2.1
RX: J2.3, JP11.3 (B), JP14.3 (B)
SOLENOID_CONTROL: JP12.3 (B), JP15.3 (B), R2.2
SW41B: D41.2 (A), SWLH_ROT1.S2
TX: J2.4, JP10.3 (B), JP13.3 (B)
VCC: J2.2, JP12.1 (A), JP15.1 (A)
col0: MCU1.16 (15), SW0.6, SW10.6, SW20.6, SW30.6, SW40.6, SW50.6
col1: MCU1.20 (29), SW1.6, SW11.6, SW21.6, SW31.6, SW51.6, SWLH_ROT1.S1
col2: MCU1.4 (3), SW2.6, SW12.6, SW22.6, SW32.6, SW42.6, SW52.6
col3: MCU1.19 (28), SW3.6, SW13.6, SW23.6, SW33.6, SW43.6, SW53.6
col4: MCU1.5 (4), SW4.6, SW14.6, SW24.6, SW34.6, SW44.6, SW54.6
col5: MCU1.18 (27), SW5.6, SW15.6, SW25.6, SW35.6, SW45.6, SW55.6
col6: MCU1.6 (5), SW6.6, SW16.6, SW26.6, SW36.6, SW46.6, SW56.6
col7: MCU1.17 (26), SW7.6, SW17.6, SW27.6, SW37.6, SW47.6, SW57.6
col8: MCU1.14 (13), SW08.6, SW18.6, SW28.6, SW38.6, SW48.6, SW58.6
encA: MCU1.15 (14), SWLH_ROT1.A
encB: MCU1.8 (7), SWLH_ROT1.B
row0: D0.1 (K), D1.1 (K), D2.1 (K), D3.1 (K), D4.1 (K), D5.1 (K), D6.1 (K), D7.1 (K), D08.1 (K), MCU1.7 (6)
row1: D10.1 (K), D11.1 (K), D12.1 (K), D13.1 (K), D14.1 (K), D15.1 (K), D16.1 (K), D17.1 (K), D18.1 (K), MCU1.9 (8)
row2: D20.1 (K), D21.1 (K), D22.1 (K), D23.1 (K), D24.1 (K), D25.1 (K), D26.1 (K), D27.1 (K), D28.1 (K), MCU1.13 (12)
row3: D30.1 (K), D31.1 (K), D32.1 (K), D33.1 (K), D34.1 (K), D35.1 (K), D36.1 (K), D37.1 (K), D38.1 (K), MCU1.12 (11)
row4: D40.1 (K), D41.1 (K), D42.1 (K), D43.1 (K), D44.1 (K), D45.1 (K), D46.1 (K), D47.1 (K), D48.1 (K), MCU1.11 (10)
row5: D50.1 (K), D51.1 (K), D52.1 (K), D53.1 (K), D54.1 (K), D55.1 (K), D56.1 (K), D57.1 (K), D58.1 (K), MCU1.10 (9)

Notes on the sheet:
Alternate Solenoid socket for short wires
Todo: Thumb cluster detach? Is there a good smd option for the Solenoid resistor? Is there a female smd socket for the solenoid connection? Check Pimaroni resistor calculation and footprint size CHeck net trace sizes. (.5 for 3.3v?) Incree trcck size on vcc and GND nets Figure out VCC on Pico Figur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
Solenoid
V2 Features: RH Trackball and rotary encoder instead of Pimaroni Move arrow keys into "+" centered around "." on left hand
TRRS jack. Serial config is default Jumper must be soldered for TX/RX
Rotary Knob
